egradman/ynot-keyboard/kicad_project/doc/assets/confirm_back.jpg

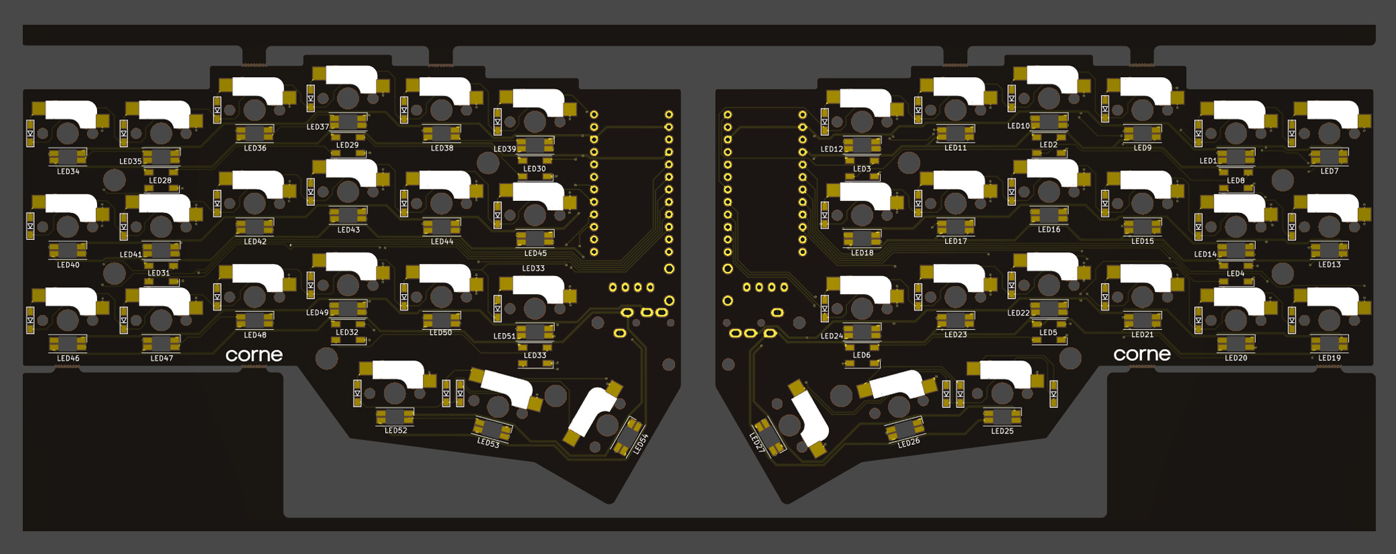
kicad_project/doc/assets/confirm_back.jpg
