egradman/ynot-keyboard/kicad_project/doc/assets/confirm_front.jpg

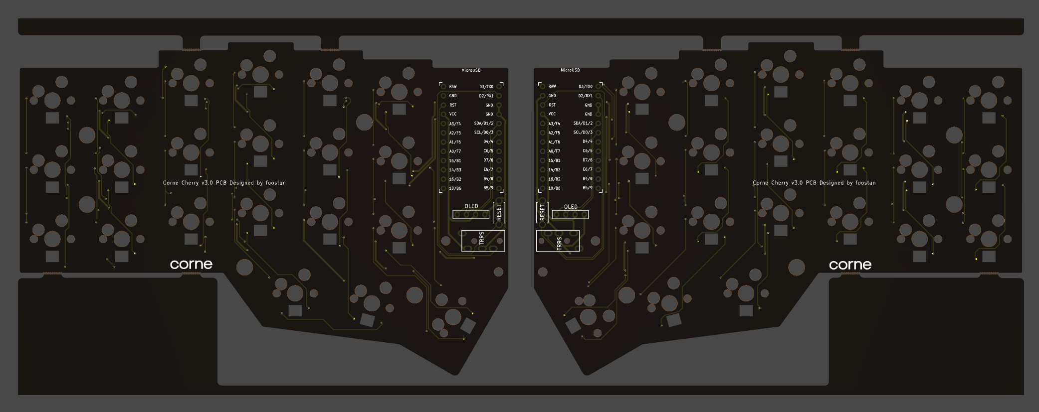
kicad_project/doc/assets/confirm_front.jpg
