egradman/ynot-keyboard/kicad_project/pcb/svg/cho-corne-ice-brd-f.png

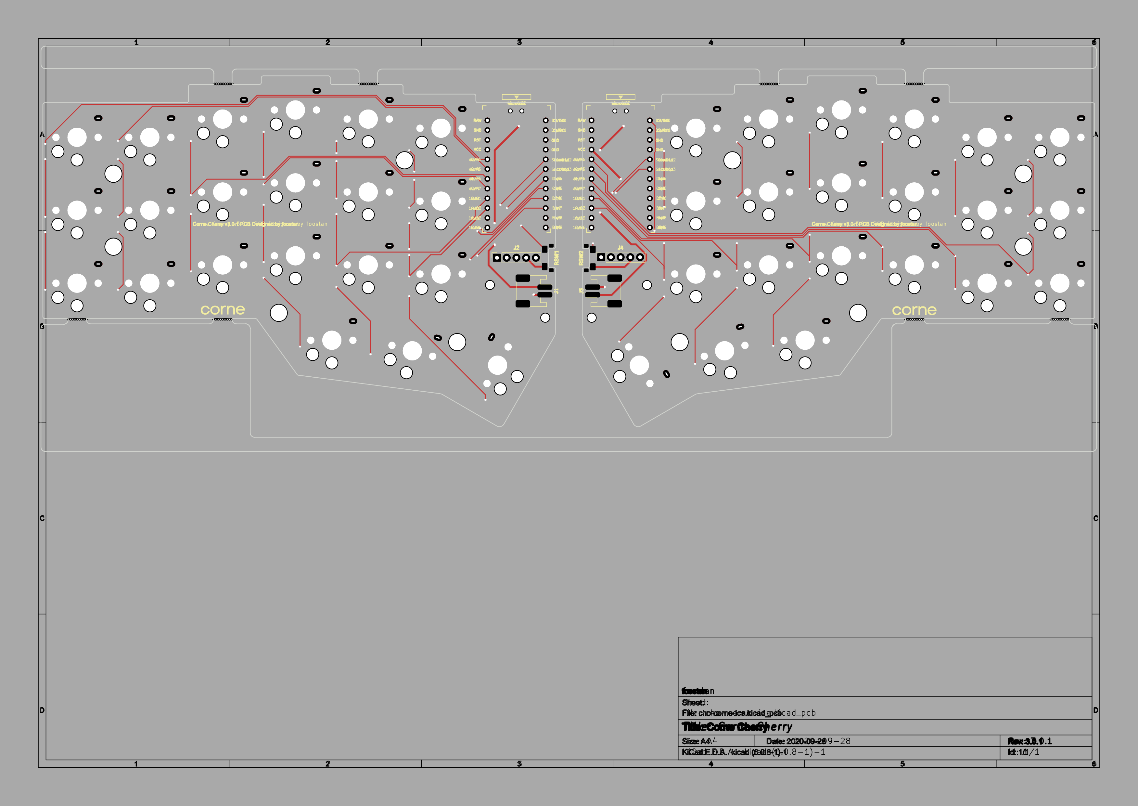
kicad_project/pcb/svg/cho-corne-ice-brd-f.png
