egradman/ynot-keyboard/kicad_project/pcb/svg/cho-corne-ice-brd.png

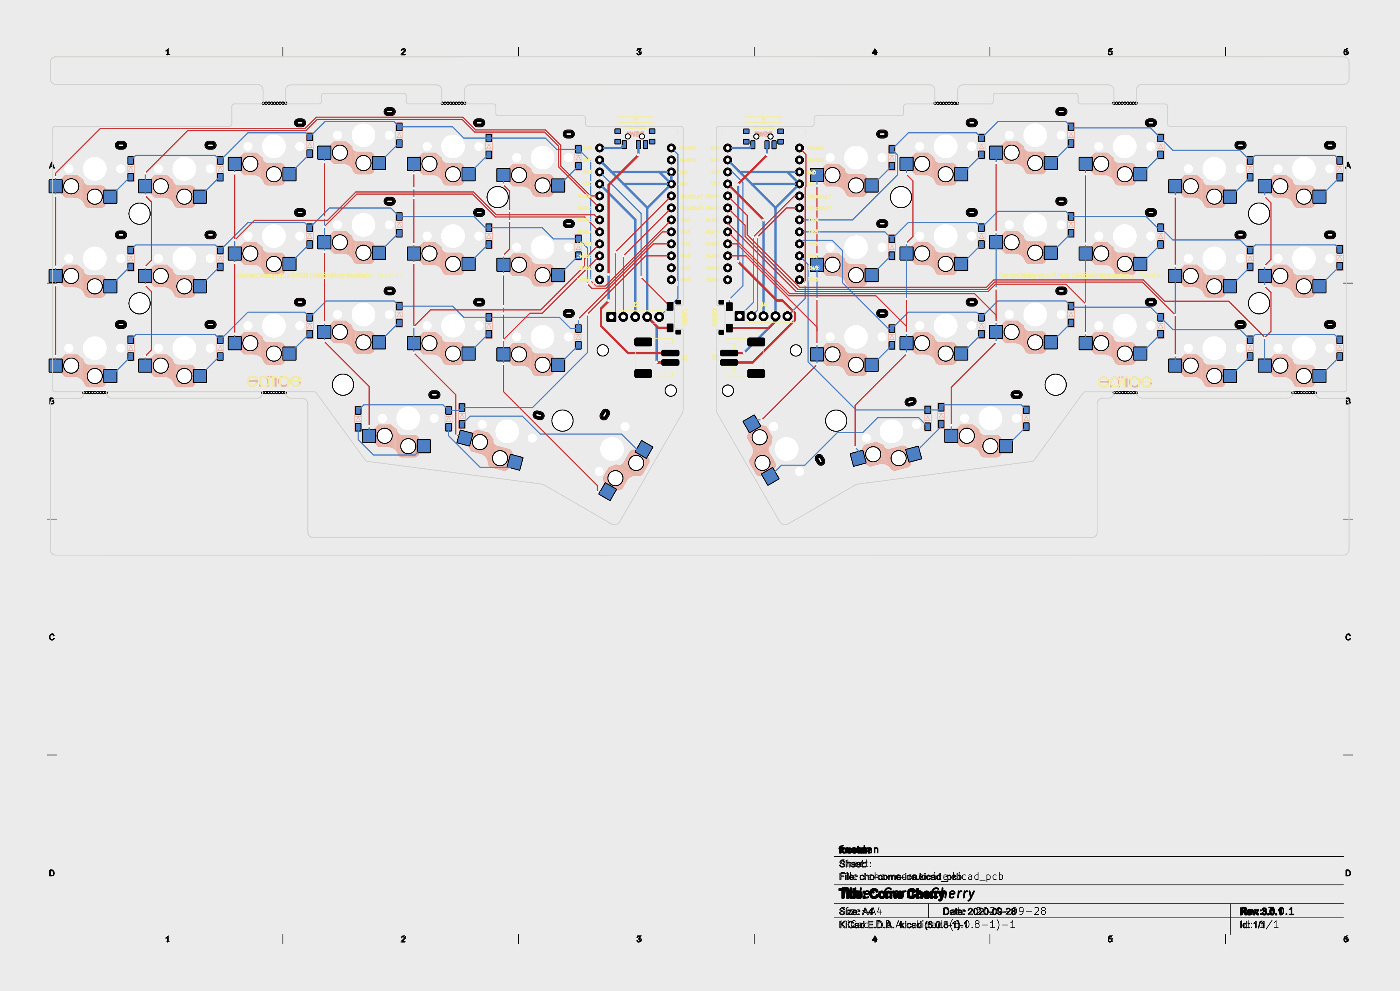
kicad_project/pcb/svg/cho-corne-ice-brd.png
