egradman/ynot-keyboard/kicad_project/pcb/svg/cho-corne-ice.png

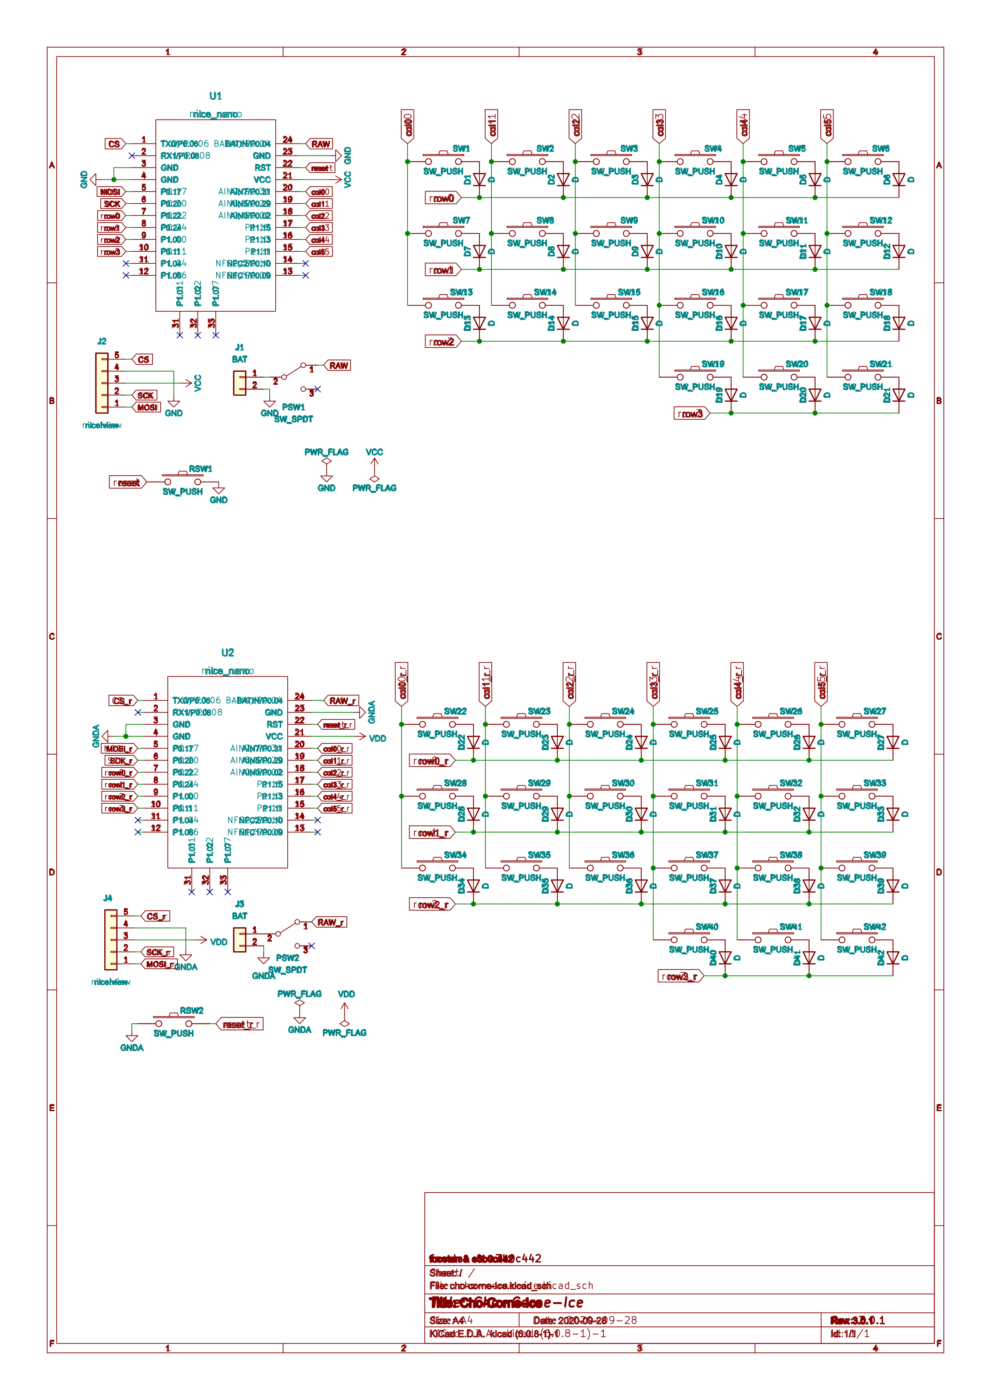
kicad_project/pcb/svg/cho-corne-ice.png
