egradman/ynot-keyboard/kicad_project/doc/assets/build_led_backlight.jpg

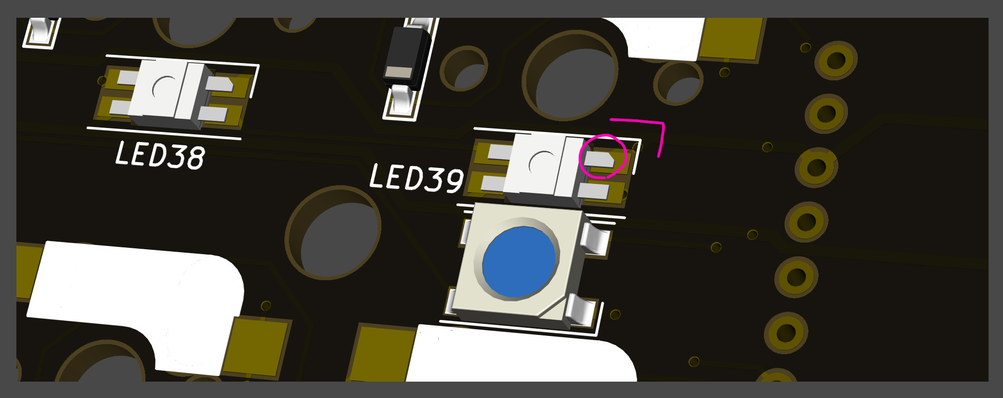
kicad_project/doc/assets/build_led_backlight.jpg
