egradman/ynot-keyboard/kicad_project/doc/assets/build_led_undergrow.jpg

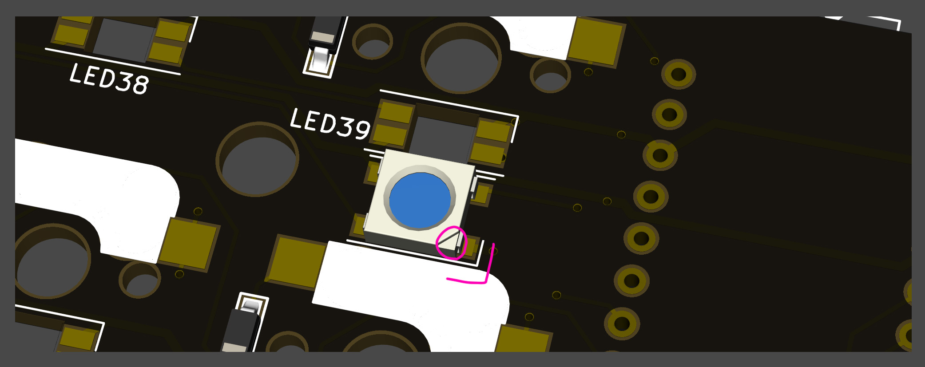
kicad_project/doc/assets/build_led_undergrow.jpg
